bondsan-github/xbox2sata/Images/IMG_4868.png

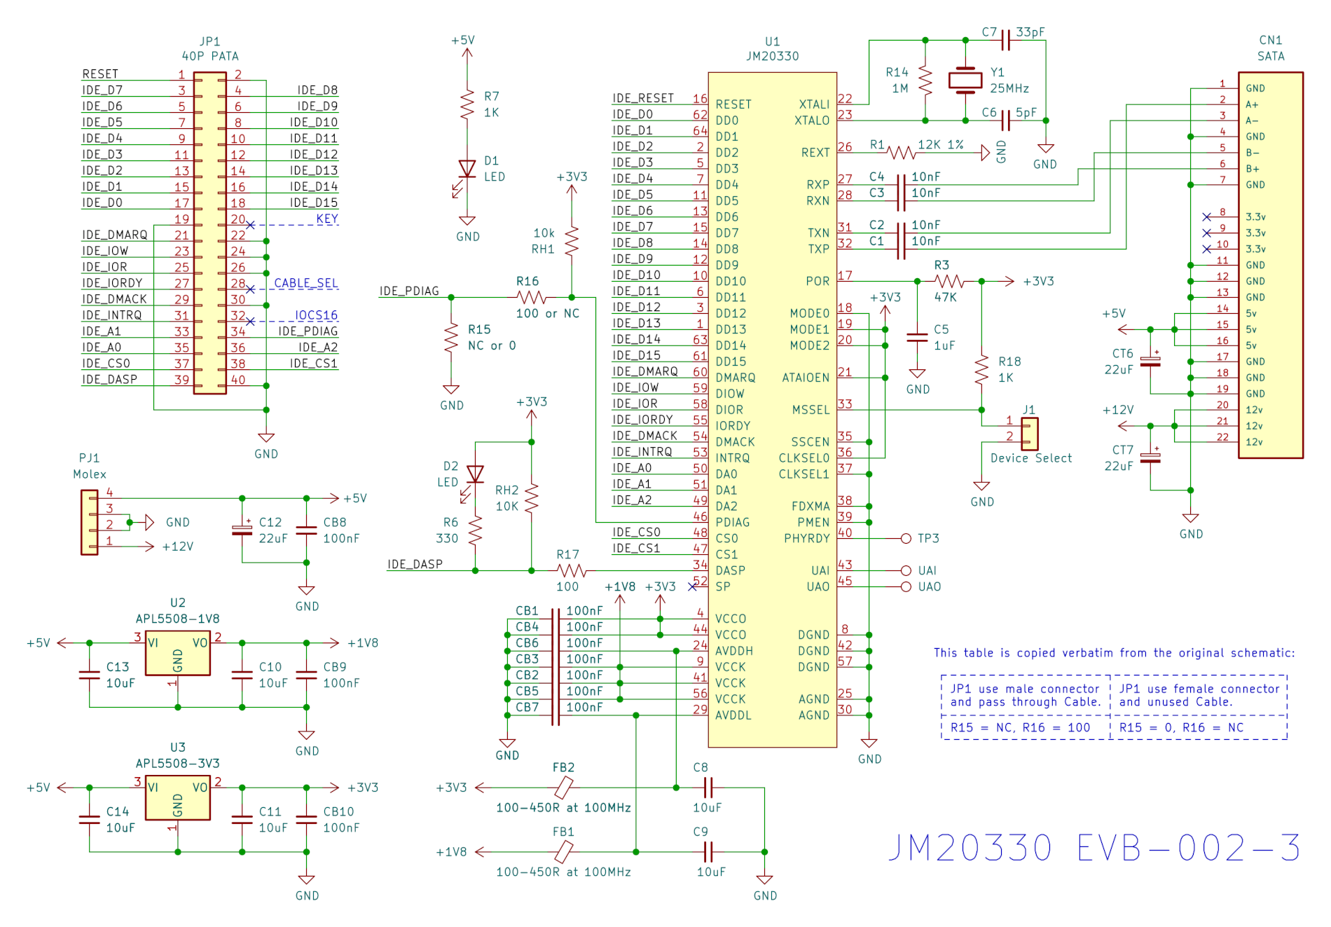
Images/IMG_4868.png
