bondsan-github/xbox2sata/Images/IMG_20240824_140928770.jpg

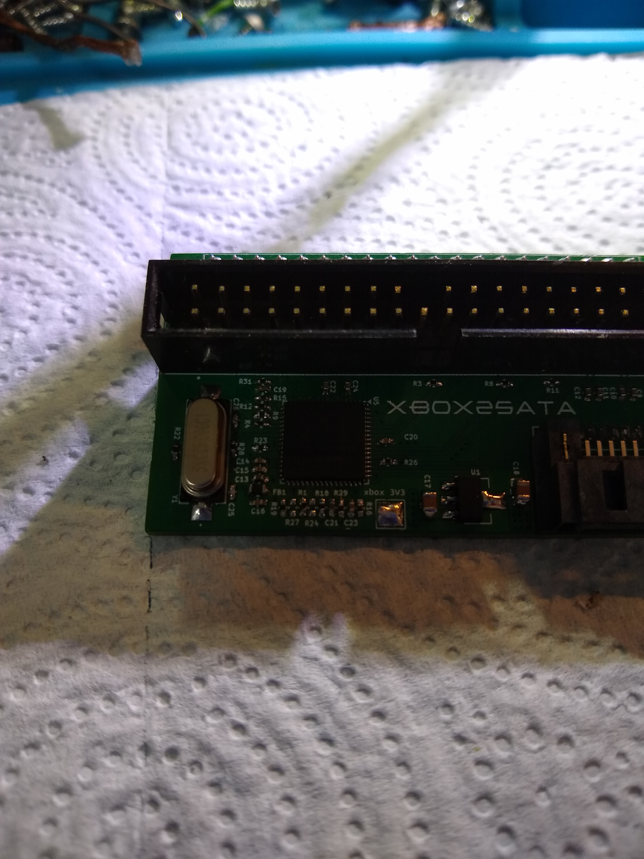
Images/IMG_20240824_140928770.jpg
