bondsan-github/xbox2sata/Images/Startech 3D view bottom.png

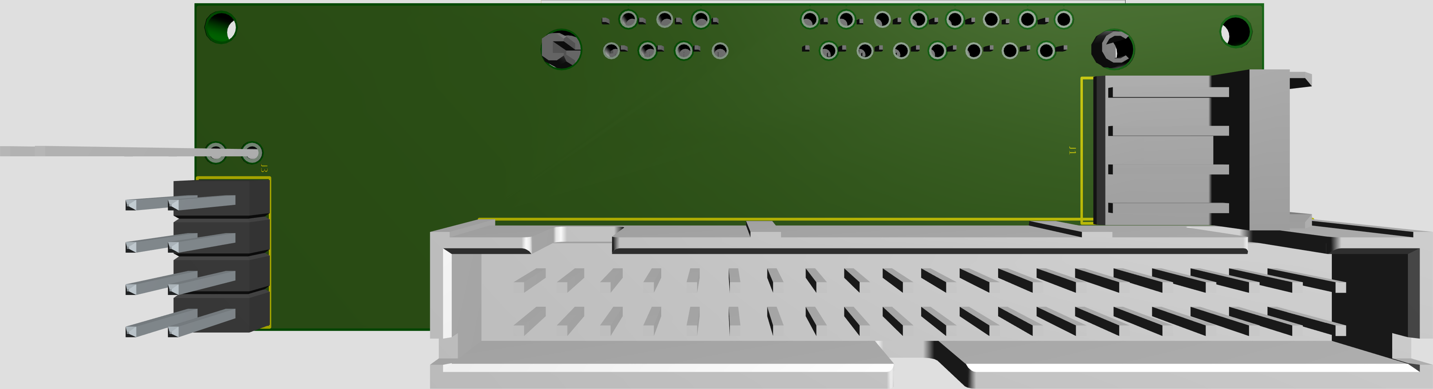
Images/Startech 3D view bottom.png
