bondsan-github/xbox2sata/Images/Startech layout top.png

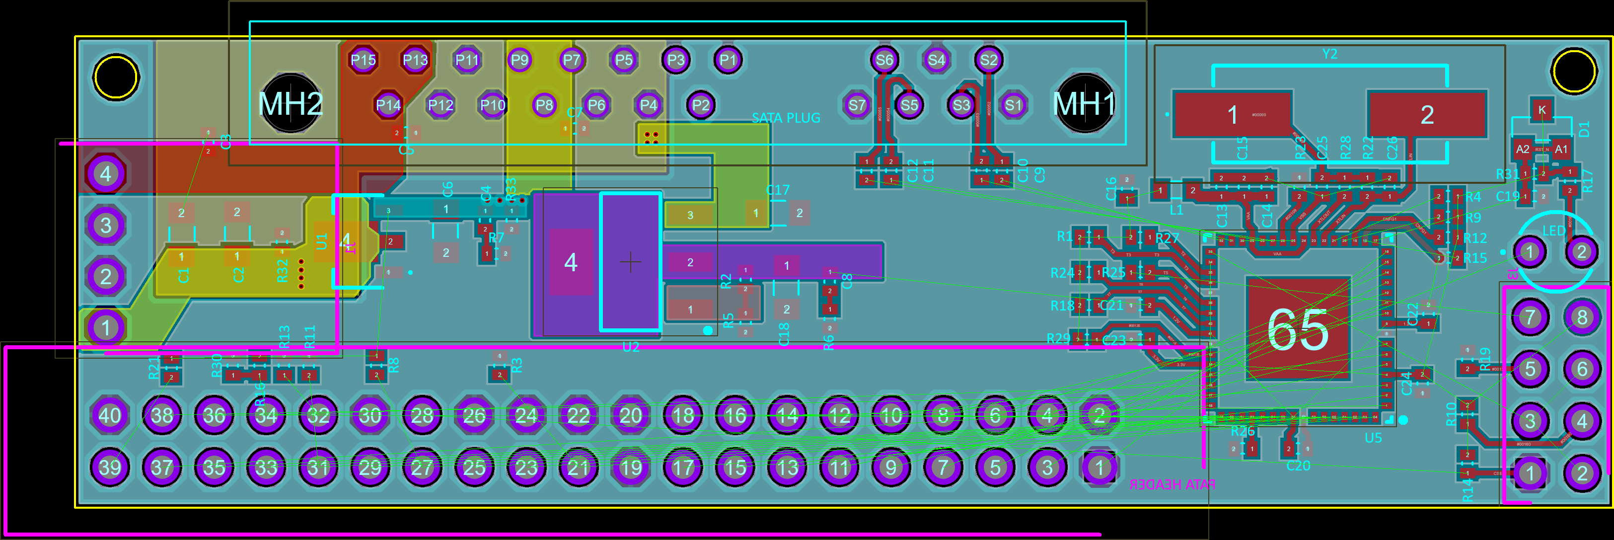
Images/Startech layout top.png
