bondsan-github/xbox2sata/Images/xbox-original-1-6-voltage-readings-top-side.webp

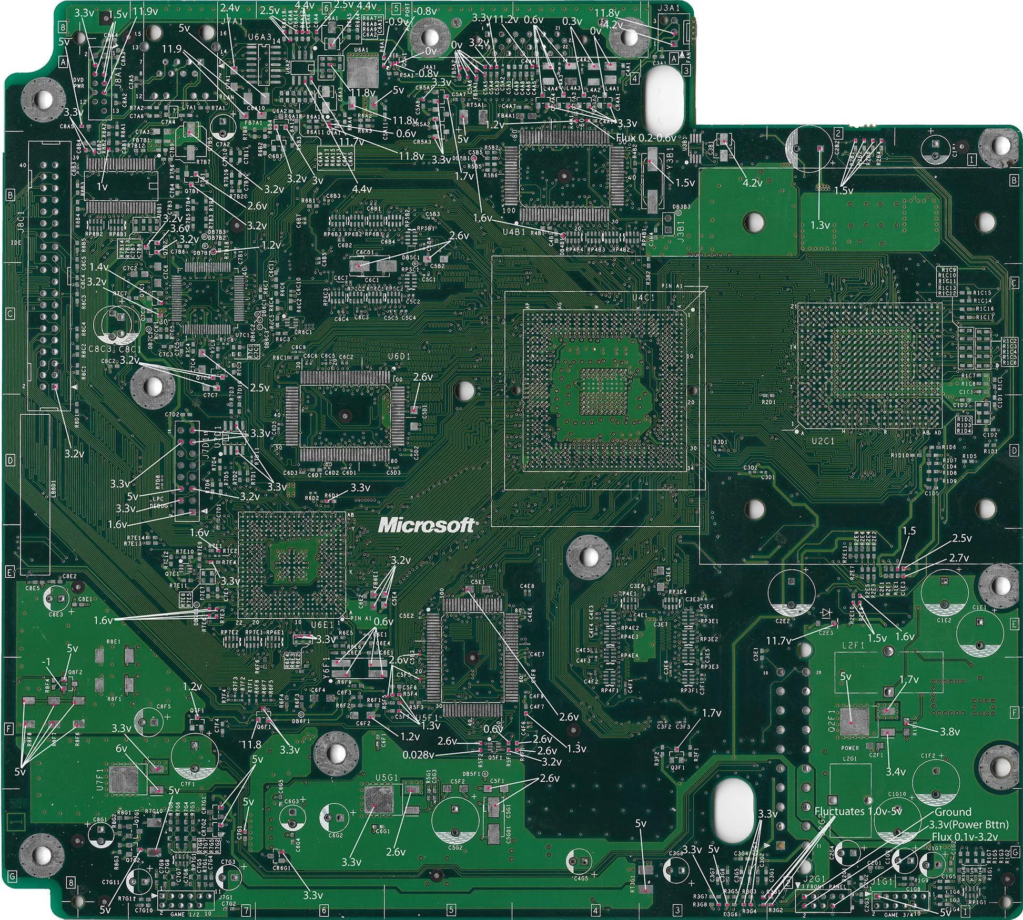
Images/xbox-original-1-6-voltage-readings-top-side.webp
